jorts64/S2miniBreakoutBoard/standalone/micropython/I2Cscan.py

from machine import I2C, Pin 
i2c = I2C(0,scl=Pin(35), sda=Pin(33))

print('Scanning I2C bus.')
devices = i2c.scan() # this returns a list of devices

device_count = len(devices)

if device_count == 0:
    print('No i2c device found.')
else:
    print(device_count, 'devices found.')

for device in devices:
    print('Decimal address:', device, ", Hex address: ", hex(device))
